bieber/capytimer/firmware/debounce.c

/*
 * Copyright (C) 2022, Robert Bieber
 *
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
 * You should have received a copy of the GNU General Public License
 * along with this program.  If not, see
 * <https://www.gnu.org/licenses/>.
 */

#include <stdint.h>

#include "adc.h"
#include "debounce.h"
#include "time.h"

uint16_t BRIGHTNESS_THRESHOLDS[4] = {204, 408, 612, 816};

struct Time debounce_minutes(struct Time existing, uint16_t adc_value);
struct Time debounce_seconds(struct Time existing, uint16_t adc_value);

struct Time debounce_time(
	struct Time existing,
	uint8_t minutes_port,
	uint8_t seconds_port
) {
	struct Time new_time = existing;
	new_time = debounce_minutes(new_time, read_adc(minutes_port));
	new_time = debounce_seconds(new_time, read_adc(seconds_port));
	return new_time;
}

struct Time debounce_minutes(struct Time existing, uint16_t adc_value) {
	uint16_t prospective = (adc_value * 11 / 1024);
	if (prospective > existing.minutes) {
		uint16_t boundary = 1024 * prospective / 11;
		if (adc_value < boundary + MINUTE_THRESHOLD) {
			return existing;
		}
	} else {
		uint16_t boundary = 1024 * existing.minutes / 11;
		if (adc_value > boundary - MINUTE_THRESHOLD) {
			return existing;
		}
	}
	existing.minutes = prospective;
	return existing;
}

struct Time debounce_seconds(struct Time existing, uint16_t adc_value) {
	uint16_t prospective = (adc_value * 12 / 1024) * 5;
	if (prospective > existing.seconds) {
		uint16_t boundary = 1024 * prospective / 60;
		if (adc_value < boundary + SECOND_THRESHOLD) {
			return existing;
		}
	} else {
		uint16_t boundary = 1024 * existing.seconds / 60;
		if (adc_value > boundary - SECOND_THRESHOLD) {
			return existing;
		}
	}
	existing.seconds = prospective;
	return existing;
}

uint8_t debounce_brightness(uint8_t existing, uint8_t port) {
	uint16_t adc_value = read_adc(port);

	uint16_t boundary = 0;
	uint8_t bucket = 1;
	uint8_t existing_bucket = existing / 51;
	for (int i = 0; i < sizeof(BRIGHTNESS_THRESHOLDS) / 2; i++) {
		uint16_t threshold = BRIGHTNESS_THRESHOLDS[i];

		if (bucket < existing_bucket) {
			boundary = BRIGHTNESS_THRESHOLDS[i + 1];
		}

		if (adc_value > threshold) {
			bucket++;
			if (bucket > existing_bucket) {
				boundary = threshold;
			}
		}
	}

	if (bucket == existing_bucket) {
		return existing;
	} else if (bucket > existing_bucket) {
		if (adc_value < boundary + BRIGHTNESS_THRESHOLD) {
			return existing;
		}
	} else if (bucket < existing_bucket) {
		if (adc_value > boundary - BRIGHTNESS_THRESHOLD) {
			return existing;
		}
	}

	return bucket * 51;
}

uint8_t debounce_button(enum Button button) {
	static uint8_t counts[BUTTON_COUNT];
	static uint8_t last_values[BUTTON_COUNT];
	static uint8_t sent[BUTTON_COUNT];

	uint8_t value;
	switch (button) {
	case BUTTON_START:
		value = !(PORT_START & (1 << PIN_START));
		break;

	case BUTTON_STOP:
		value = !(PORT_STOP & (1 << PIN_STOP));
		break;

	case RF_START:
		value = PORT_RF_START & (1 << PIN_RF_START);
		break;

	case RF_STOP:
		value = PORT_RF_STOP & (1 << PIN_RF_STOP);
		break;
	}

	if (value == last_values[button] && counts[button] <= BUTTON_THRESHOLD) {
		counts[button]++;
	} else {
		counts[button] = 0;
		last_values[button] = value;
	}

	if (counts[button] > BUTTON_THRESHOLD) {
		if (last_values[button]) {
			if (sent[button]) {
				return 0;
			} else {
				// We only want to send a button press once until it's
				// gone back to zero
				sent[button] = 1;
				return 1;
			}
		} else {
			sent[button] = 0;
		}
	}
	return 0;
}
