bieber/capytimer/firmware/setup.c

/*
 * Copyright (C) 2022, Robert Bieber
 *
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
 * You should have received a copy of the GNU General Public License
 * along with this program.  If not, see
 * <https://www.gnu.org/licenses/>.
 */

#include <avr/interrupt.h>

#include "setup.h"

void setup(uint8_t pixels[SCREEN_SIZE]) {
	for (int i = 0; i < SCREEN_SIZE; i++) {
		pixels[i] = 0;
	}

	// Clear out all the DDR and PORT registers
	DDR_STATUS = 0;
	DDR_SCREEN = 0;
	DDR_BUZZ = 0;
	DDR_START = 0;
	DDR_STOP = 0;
	DDR_RF_START = 0;
	DDR_RF_STOP = 0;
	DDR_DIAGNOSTIC = 0;
	PULLUP_START = 0;
	PULLUP_STOP = 0;
	PULLUP_RF_START = 0;
	PULLUP_RF_STOP = 0;
	PULLUP_DIAGNOSTIC = 0;

	// Set outputs and pullups on the input ports
	DDR_STATUS |= (1 << PIN_STATUS);
	DDR_SCREEN |= (1 << PIN_SCREEN);
	DDR_BUZZ |= (1 << PIN_BUZZ);
	PULLUP_START |= (1 << PIN_START);
	PULLUP_STOP |= (1 << PIN_STOP);
	PULLUP_DIAGNOSTIC |= (1 << PIN_DIAGNOSTIC);

	// Use AVCC for ADC reference
    ADMUX = (1<<REFS0);
	// Enable ADC and set f/128 prescaler for accuracy
    ADCSRA = (1<<ADEN) | (1<<ADPS2) | (1<<ADPS1) | (1<<ADPS0);

	// Timer 0 operates in CTC mode and counts off approximate
	// 10ms increments for the rest time display
	TCCR0A |= (1 << WGM01);
	TIMSK0 |= (1 << OCIE0A);
	OCR0A = 200;

	// Timer 1 operates in CTC mode counting off seconds for the main
	// timer
	TCCR1B |= (1 << WGM12);
	TIMSK1 |= (1 << OCIE1A);
	OCR1A = 19531;

	// Timer 2 operates in CTC mode and counts off approximate 10ms
	// increments for the buzzer
	TCCR2A |= (1 << WGM21);
	TIMSK2 |= (1 << OCIE2A);
	OCR2A = 200;

	// Turn on interrupts
	sei();

	// Turn on status light on startup
	PORT_STATUS |= (1 << PIN_STATUS);
}
